AverseABFun/BrainHat/img_0281.jpg

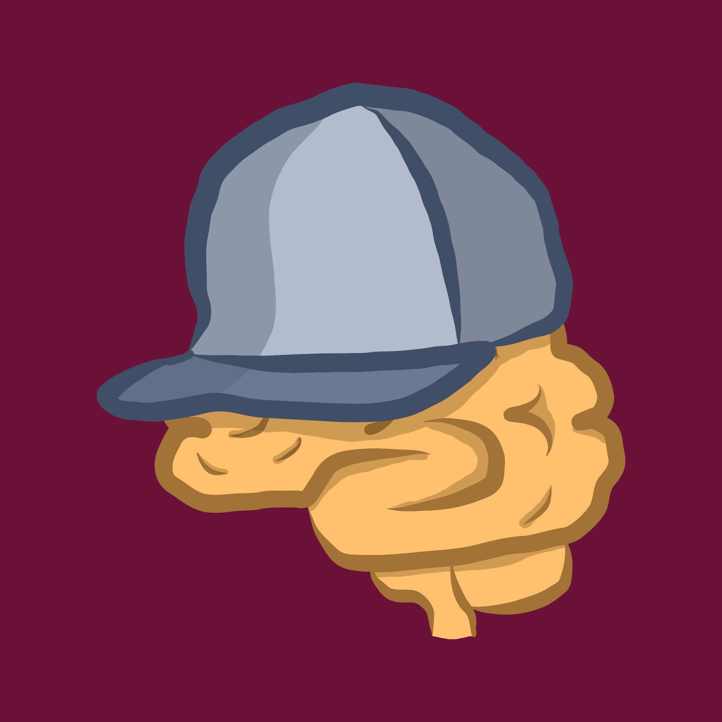
img_0281.jpg
